Acliad/WALL-E-Software/src/walle/src/display/animate_solar_panel.cpp

/**
 * @file animate_solar_panel.cpp
 * @author Isaac Rex (@Acliad)
 * @brief This file contains the implementation of the AnimateSolarPanel class. This class is used to animate the solar
 * panel by turning on and off the bars in a sequence of keyframes.
 * @version 0.1
 * @date 2024-02-19
 * 
 * @copyright Copyright (c) 2024
 * 
 */
#include "animate_solar_panel.hpp"

AnimateSolarPanel::AnimateSolarPanel()
    : first_keyframe(nullptr), current_keyframe(nullptr), last_keyframe(nullptr), last_update_time_ms(0),
      solar_panel(nullptr), num_bars_on(0), show_sun(false), running(false), time_between_bar_updates_ms(0),
      num_bars_to_update(0), incrementing(false) {
}

void AnimateSolarPanel::addKeyframe(int num_bars_on, unsigned int duration_ms, bool show_sun) {
    addKeyframe(num_bars_on, duration_ms, 0, nullptr, show_sun);
}

void AnimateSolarPanel::addKeyframe(int num_bars_on, unsigned int duration_ms, unsigned int track_index, DfMp3 *dfmp3,
                                    bool show_sun) {
    // Creates Keyframe from the arguments and add it to the animation.
    Keyframe *new_keyframe = new Keyframe;
    for (int i = 0; i < _SOLAR_PANEL_NUM_BARS; i++) {
        new_keyframe->bar_status[i] = i < num_bars_on;
    }
    new_keyframe->show_sun = show_sun;
    new_keyframe->duration_ms = duration_ms;
    new_keyframe->next = nullptr;
    new_keyframe->track_index = track_index;
    new_keyframe->dfmp3 = dfmp3;

    this->_appendKeyframe(new_keyframe);
}

void AnimateSolarPanel::addKeyframeFromArray(bool bar_status[_SOLAR_PANEL_NUM_BARS], unsigned int duration_ms, bool show_sun) {
    addKeyframeFromArray(bar_status, duration_ms, 0, nullptr, show_sun);
}

void AnimateSolarPanel::addKeyframeFromArray(bool bar_status[_SOLAR_PANEL_NUM_BARS], unsigned int duration_ms,
                                             unsigned int track_index, DfMp3 *dfmp3, bool show_sun) {
    // Creates Keyframe from the arguments and add it to the animation.
    Keyframe *new_keyframe = new Keyframe;
    for (int i = 0; i < _SOLAR_PANEL_NUM_BARS; i++) {
        new_keyframe->bar_status[i] = bar_status[i];
    }
    new_keyframe->show_sun = show_sun;
    new_keyframe->duration_ms = duration_ms;
    new_keyframe->next = nullptr;
    new_keyframe->track_index = track_index;
    new_keyframe->dfmp3 = dfmp3;

    this->_appendKeyframe(new_keyframe);
}

void AnimateSolarPanel::addPauseKeyframe(unsigned int duration_ms) {
    addPauseKeyframe(duration_ms, 0, nullptr);
}

void AnimateSolarPanel::addPauseKeyframe(unsigned int duration_ms, unsigned int track_index, DfMp3 *dfmp3) {
    // Pauses the animation for the given duration. This is done by adding a keyframe with the same bar status as the
    // current keyframe and the given duration.
    // Find the last keyframe
    Keyframe* keyframe = this->first_keyframe;
    while(keyframe->next != nullptr) {
        keyframe = keyframe->next;
    }
    this->addKeyframeFromArray(keyframe->bar_status, duration_ms);
}

void AnimateSolarPanel::_appendKeyframe(Keyframe *new_keyframe) {
    // If the keyframe is the first Keyframe in the animation, set it as the first keyframe and the current keyframe.
    // Otherwise, add it to the end of the animation.
    if (this->first_keyframe == nullptr) {
        this->first_keyframe = new_keyframe;
        this->current_keyframe = new_keyframe;
    } else {
        Keyframe *keyframe = this->first_keyframe;
        // We could also track a tail pointer to avoid this loop. Not too concerned about speed, so save the memory.
        while (keyframe->next != nullptr) {
            keyframe = keyframe->next;
        }
        keyframe->next = new_keyframe;
    }
}

void AnimateSolarPanel::start() {
    // Start the animation by setting the current keyframe to the first keyframe and setting the running flag to true.
    this->current_keyframe = this->first_keyframe;
    this->last_keyframe = this->first_keyframe;
    this->last_update_time_ms = millis();
    this->time_between_bar_updates_ms = this->current_keyframe->duration_ms;
    // Force all the bars to match the first keyframe. Could use
    // solar_panel->setAllBars(this->current_keyframe->bar_status) but we also want to count the number of bars on so
    // loop manually.
    this->num_bars_on = 0;
    for(int i = 0; i < _SOLAR_PANEL_NUM_BARS; i++) {
        this->solar_panel->setBar(i, this->current_keyframe->bar_status[i]);
        this->num_bars_on += this->current_keyframe->bar_status[i];
    }
    this->solar_panel->setSun(this->current_keyframe->show_sun);
    this->running = true;
}

void AnimateSolarPanel::stop() {
    // Stop the animation by setting the running flag to false.
    this->running = false;
}

void AnimateSolarPanel::update() {
    // First, check if we're running. If we're not, do nothing. Then see if the current keyfram is the same as the last
    // keyframe (current_keyframe is incremented when a keyframe finishes). If it is, check if the bars need to be
    // updated. If they do, update them. If it is not, calculate the time between each bar update and determine if we
    // are incrementing or decrementing the bars.

    if(this->isRunning()) {
        // If the current keyframe is the same as the last keyframe, we're still updating the bars for this keyframe.
        if(this->current_keyframe == this->last_keyframe) {
            // Check if enough time has passeded to update the bars.
            if (millis() - this->last_update_time_ms >= this->time_between_bar_updates_ms) {
                this->_updateBars();
                // Check if the keyframe is over
                if (this->num_bars_to_update <= 0) { // Will be less than 0 if it started at 0 (e.g., a pause frame)
                    this->last_keyframe = this->current_keyframe;
                    this->current_keyframe = this->current_keyframe->next;
                    if (this->current_keyframe == nullptr) {
                        this->stop();
                    }
                }
            }
        } else {
            // If the current keyframe is not the same as the previous keyframe, we've transistioned to a new keyframe.
            // Calculated how many bars changed from the previous keyframe to the current keyframe and if we're
            // incrementing or decrementing the bars. Then, determine the number of milliseconds between each bar. We
            // also need to update the last_keyframe to the current_keyframe.
            this->num_bars_to_update = // Is < 0 if decrementing
                this->_getNumberOfBarsToUpdate(this->last_keyframe->bar_status, this->current_keyframe->bar_status);
            this->incrementing = this->num_bars_to_update >= 0;
            this->num_bars_to_update = abs(this->num_bars_to_update); // Fix the sign
            // Could segfault if num_bars_to_update = 0 and we still want to way for duration_ms to pass, so set 1 as 
            // the minimum divide by value here. This forces time_between_bar_updates_ms to be equal to duration_ms if
            // there are no bars to update. Subtracting 1 since we'll immediately update the bars once.
            this->time_between_bar_updates_ms =
                this->current_keyframe->duration_ms / max(this->num_bars_to_update - 1, 1);

            // Set the sun status
            this->solar_panel->setSun(this->current_keyframe->show_sun);
            this->last_keyframe = this->current_keyframe;
            // Update bars for start of frame
            this->_updateBars();

            // Play the requested track, if any
            if (this->current_keyframe->dfmp3 != nullptr) {
                this->current_keyframe->dfmp3->playMp3FolderTrack(this->current_keyframe->track_index);
            }
        }
    }
}

void AnimateSolarPanel::_updateBars() {
    if (this->incrementing && this->num_bars_to_update > 0) {
        this->solar_panel->setBar(this->num_bars_on, true);
        this->num_bars_on++;
    } else if (this->num_bars_to_update > 0) {
        // need to subtract 1 from num_bars_on otherwise it turns off the bar above the last bar that was
        // turned on. Don't have to do this for incrementing case because we are trying to turn on the bar
        // above the last bar that was turned on.
        this->solar_panel->setBar(this->num_bars_on - 1, false);
        this->num_bars_on--;
    }
    this->num_bars_to_update--;
    this->last_update_time_ms = millis();
}

Keyframe *AnimateSolarPanel::getCurrentKeyframe() { 
    return this->current_keyframe; 
}

void AnimateSolarPanel::setSolarPanel(SolarPanel *solar_panel) {
    this->solar_panel = solar_panel;
}

bool AnimateSolarPanel::isRunning() { 
    return this->running; 
}

void AnimateSolarPanel::updateKeyframe(unsigned int index, bool bar_status[_SOLAR_PANEL_NUM_BARS],
                                       unsigned int duration_ms) {
    // Update the keyframe at the given index with the given values.
    // Create the new keyframe
    Keyframe* new_keyframe = new Keyframe;
    for(int i = 0; i < _SOLAR_PANEL_NUM_BARS; i++) {
        new_keyframe->bar_status[i] = bar_status[i];
    }
    new_keyframe->duration_ms = duration_ms;
    new_keyframe->next = nullptr;

    // Find the keyframe at the given index and update it. If the keyframe is the first keyframe, update it and set it
    // as the first keyframe. Otherwise, find the keyframe before it and update it. 
    if(index == 0) {
        new_keyframe->next = this->first_keyframe->next;
        this->first_keyframe = new_keyframe;
    } else {
        Keyframe* temp_keyframe = this->first_keyframe;
        // Need to start at i = 1 because we already have the first keyframe, so if i = 0, we will be one keyframe
        // ahead. We need index - 1 because we need to stop at the keyframe before the one we want to update. 
        for(int i = 1; i < index-1; i++) {
            temp_keyframe = temp_keyframe->next;
        }
        new_keyframe->next = temp_keyframe->next->next;
        temp_keyframe->next = new_keyframe;
    }
}

int AnimateSolarPanel::_getNumberOfBarsToUpdate(bool last_bar_status[_SOLAR_PANEL_NUM_BARS], bool current_bar_status[_SOLAR_PANEL_NUM_BARS]) { 
    // Returns the difference in the number of bars there are on between last_bar_status and current_bar_status. Returns
    // a negative value if there are more bars on in last_bar_status than current_bar_status (i.e., decrementing)
    int num_bars_on = 0;
    for(int i = 0; i < _SOLAR_PANEL_NUM_BARS; i++) {
        num_bars_on += current_bar_status[i] - last_bar_status[i];
    }

    return num_bars_on;
}
