Acliad/WALL-E-Software/src/walle/solar_animations.hpp

#ifndef SOLAR_ANIMATIONS_HPP
#define SOLAR_ANIMATIONS_HPP
#include "src/display/animate_level.hpp"

extern AnimateLevel animate_display_startup;

namespace DisplayAnimations {
    void setup_animations();
}

#endif // SOLAR_ANIMATIONS_HPP
